zredlined/probe-gt-gauge-cluster-enclosure/reference/cage_scan/steering_support_detail_reference.png

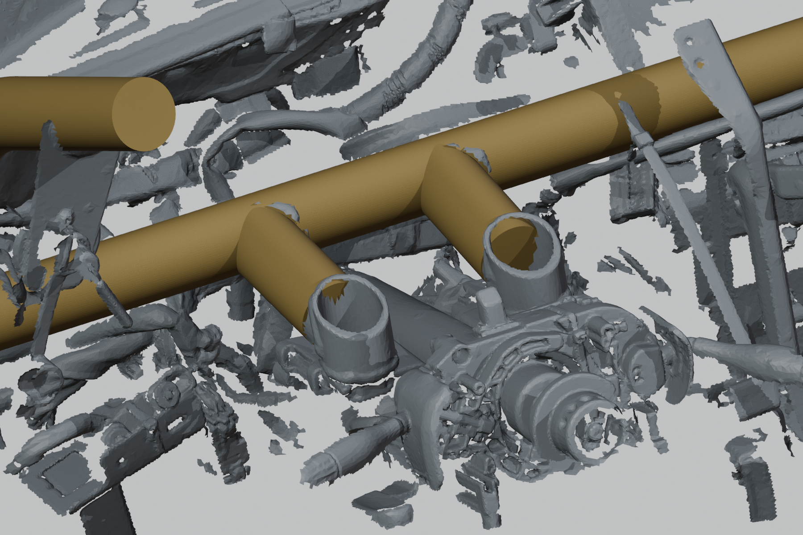
reference/cage_scan/steering_support_detail_reference.png
