zredlined/probe-gt-gauge-cluster-enclosure/reference/cage_scan/top_view_reference.png

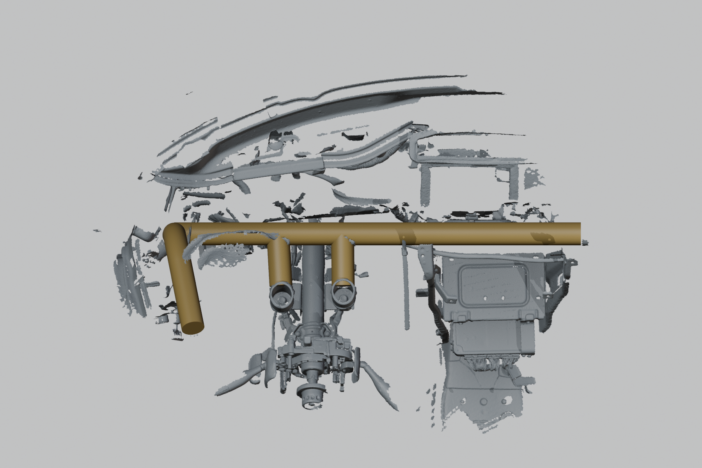
reference/cage_scan/top_view_reference.png
