zredlined/probe-gt-gauge-cluster-enclosure/reference/cluster_scan/mounting_hole_fits.png

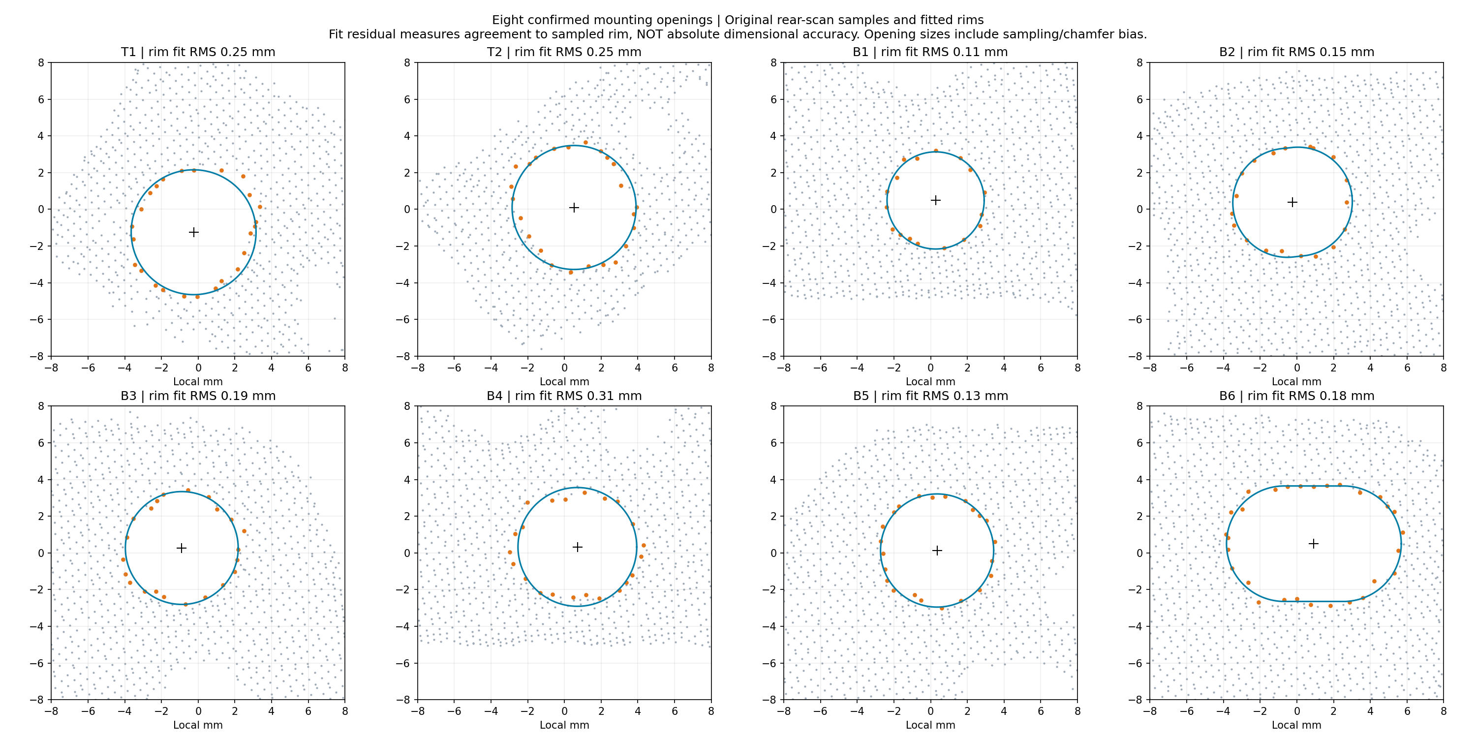
reference/cluster_scan/mounting_hole_fits.png
