zredlined/probe-gt-gauge-cluster-enclosure/reference/cluster_scan/mounting_holes_identification.png

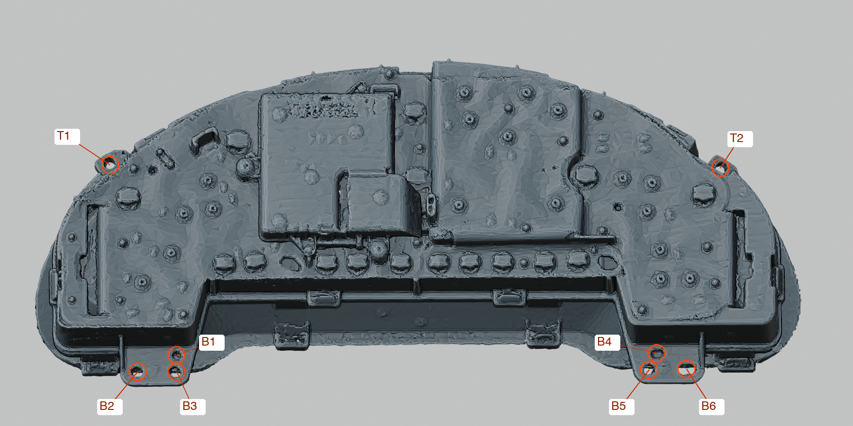
reference/cluster_scan/mounting_holes_identification.png
