zredlined/probe-gt-gauge-cluster-enclosure/stl/shell_L.stl

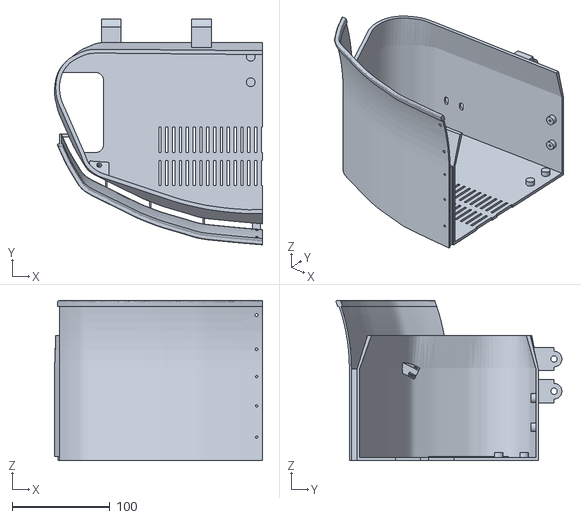
[picture p31: CAD file, 2026-10-02]
stl/shell_L.stl
213.1 x 231.3 x 164.0
