zredlined/probe-gt-gauge-cluster-enclosure/stl/test/test_coupon.stl

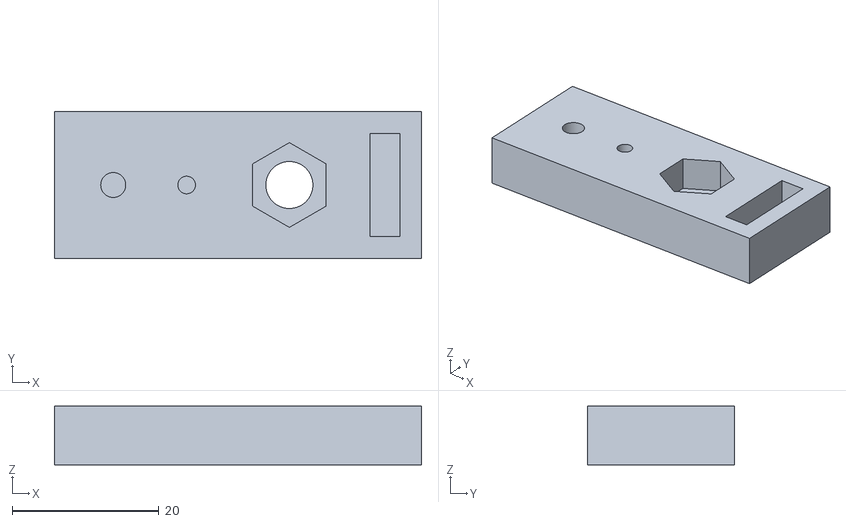
[picture p32: CAD file, 2026-09-27]
stl/test/test_coupon.stl
50.0 x 20.0 x 8.00
