zredlined/probe-gt-gauge-cluster-enclosure/reference/cage_scan/driver_side_steering_support_mm.stl

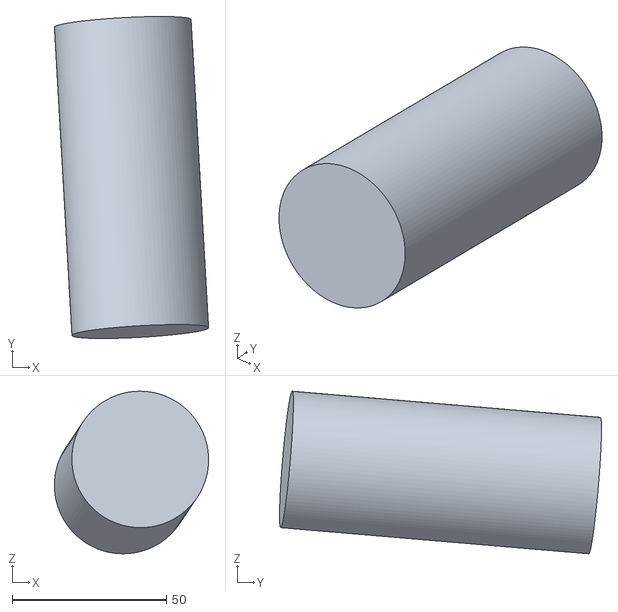
[picture p33: CAD file, 2026-09-26]
reference/cage_scan/driver_side_steering_support_mm.stl
50.1 x 104.5 x 52.8
