zredlined/probe-gt-gauge-cluster-enclosure/stl/shell_R.stl

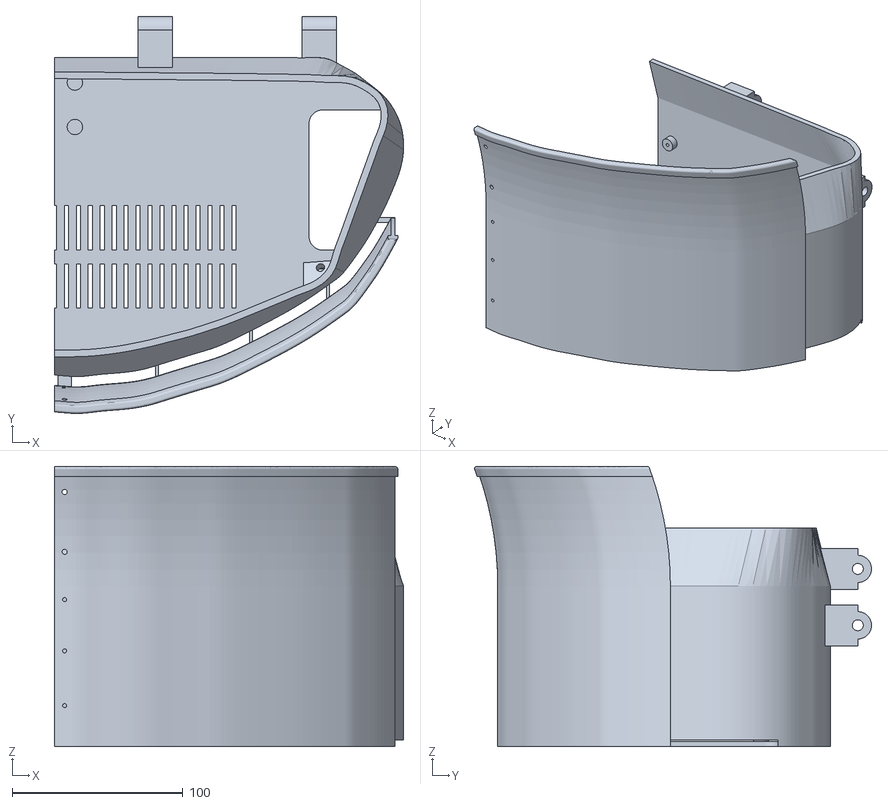
[picture p34: CAD file, 2026-10-02]
stl/shell_R.stl
204.3 x 232.2 x 164.0
