zredlined/probe-gt-gauge-cluster-enclosure/stl/support_pieces.3mf

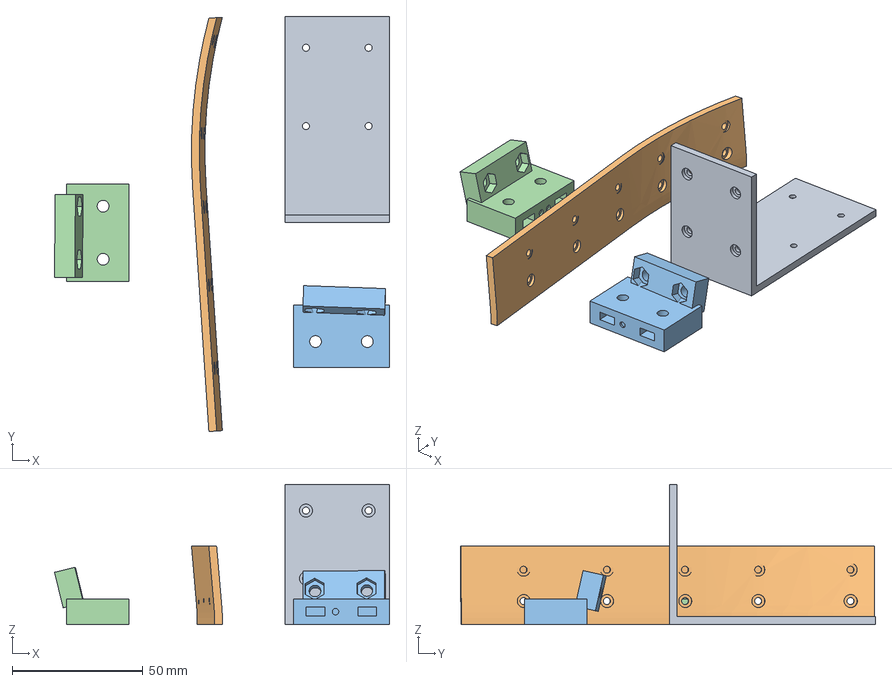
[picture p36: CAD file, 2026-10-02]
stl/support_pieces.3mf
128.3 x 159.0 x 53.7 mm
print_keel_bar.stl
print_spine_bar.stl
print_foot_lug_L.stl
print_foot_lug_R.stl
