zredlined/probe-gt-gauge-cluster-enclosure/reference/cage_scan/master_switch_region_scan_mm.stl

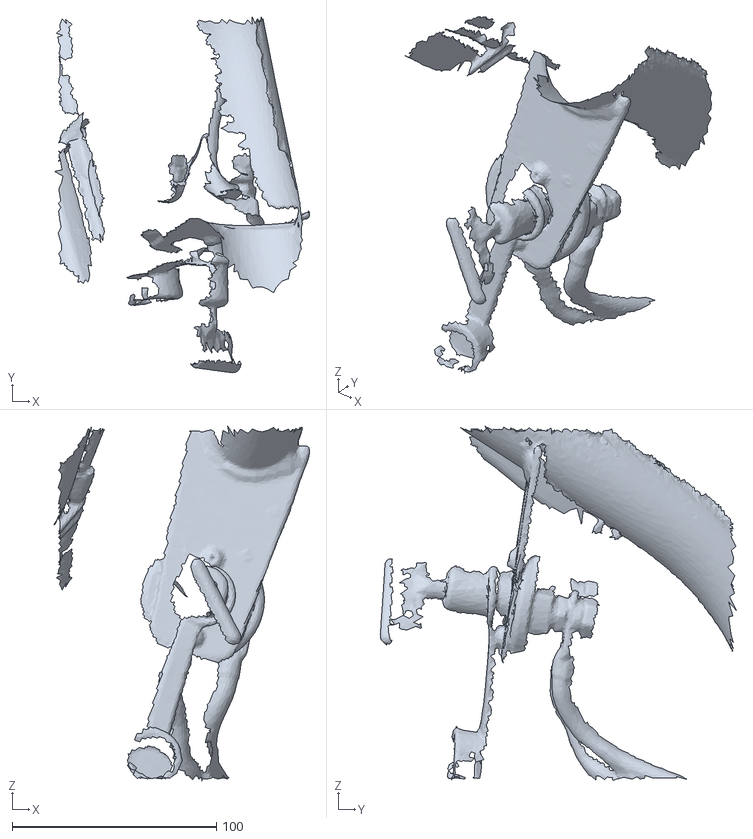
[picture p37: CAD file, 2026-09-26]
reference/cage_scan/master_switch_region_scan_mm.stl
125.0 x 174.5 x 173.8
