zredlined/probe-gt-gauge-cluster-enclosure/stl/foot_L.stl

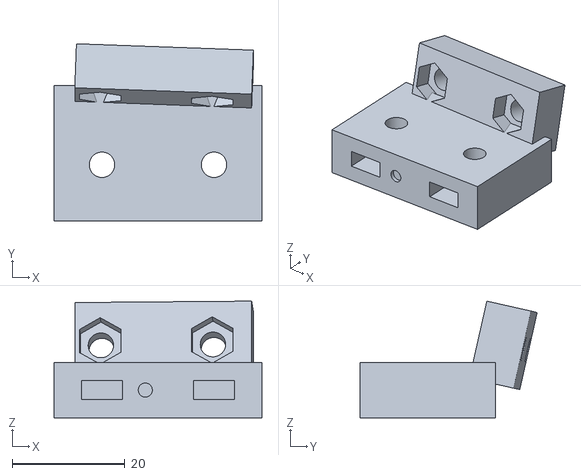
[picture p38: CAD file, 2026-09-30]
stl/foot_L.stl
36.8 x 31.4 x 20.7
