zredlined/probe-gt-gauge-cluster-enclosure/reference/cage_scan/cage_dash_crossbar_mm.stl

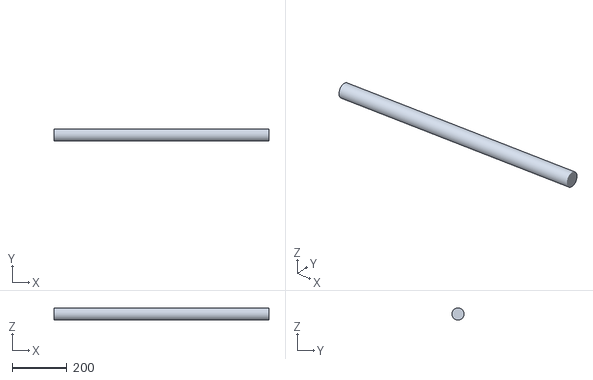
[picture p39: CAD file, 2026-09-26]
reference/cage_scan/cage_dash_crossbar_mm.stl
782.3 x 44.5 x 44.5
