zredlined/probe-gt-gauge-cluster-enclosure/stl/foot_R.stl

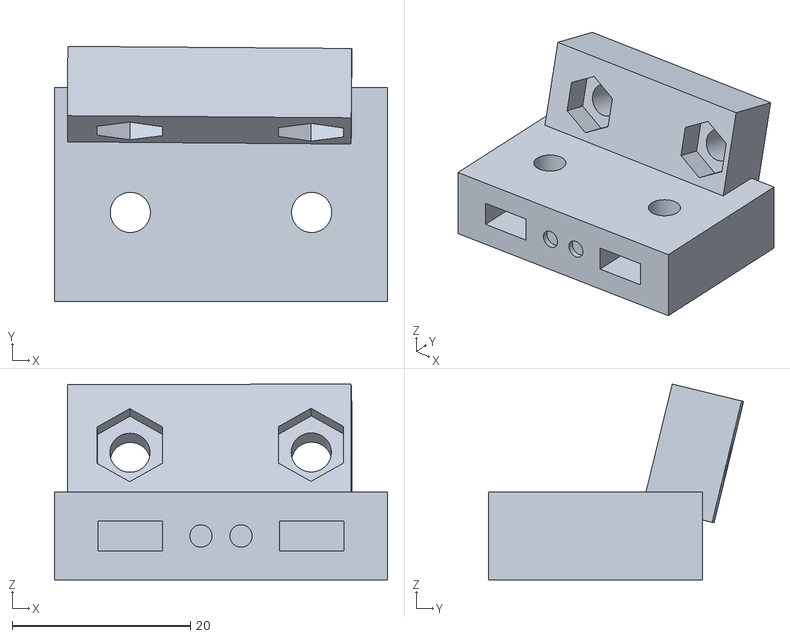
[picture p40: CAD file, 2026-09-30]
stl/foot_R.stl
37.3 x 28.6 x 22.0
