zredlined/probe-gt-gauge-cluster-enclosure/reference/cage_scan/cage_driver_upright_mm.stl

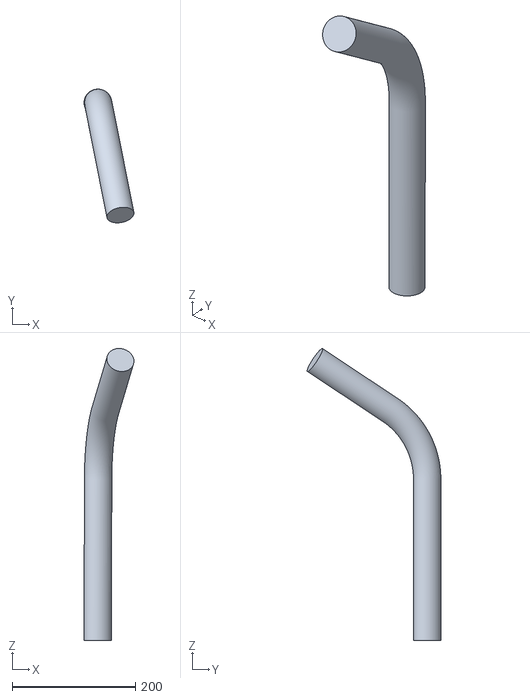
[picture p41: CAD file, 2026-09-26]
reference/cage_scan/cage_driver_upright_mm.stl
80.9 x 216.7 x 473.2
