zredlined/probe-gt-gauge-cluster-enclosure/stl/spine_bar.stl

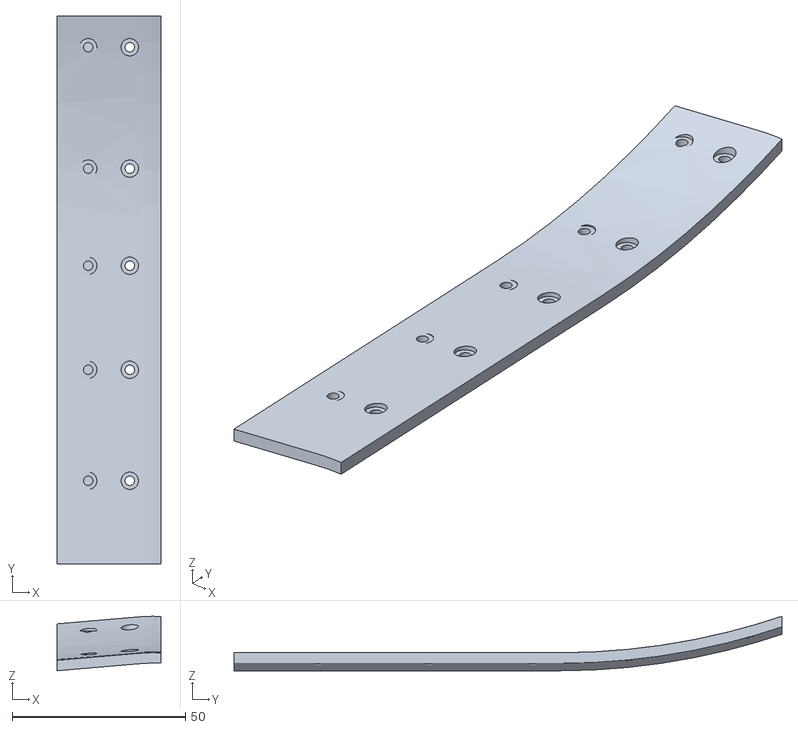
[picture p42: CAD file, 2026-09-30]
stl/spine_bar.stl
30.0 x 158.0 x 15.7
