zredlined/probe-gt-gauge-cluster-enclosure/reference/cage_scan/steering_supports_region_scan_mm.stl

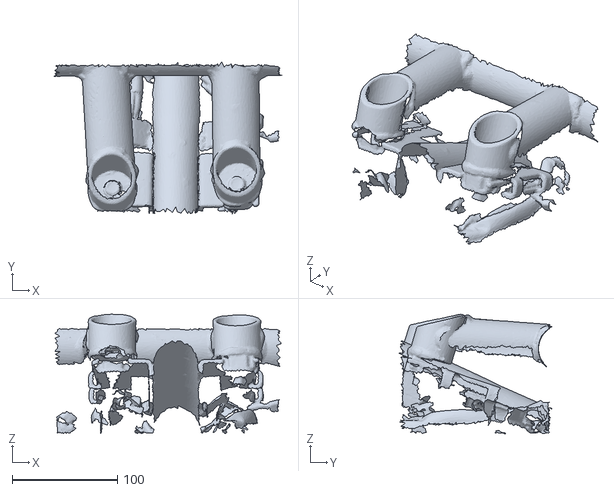
[picture p43: CAD file, 2026-09-26]
reference/cage_scan/steering_supports_region_scan_mm.stl
215.5 x 146.6 x 113.5
