zredlined/probe-gt-gauge-cluster-enclosure/stl/keel_bar.stl

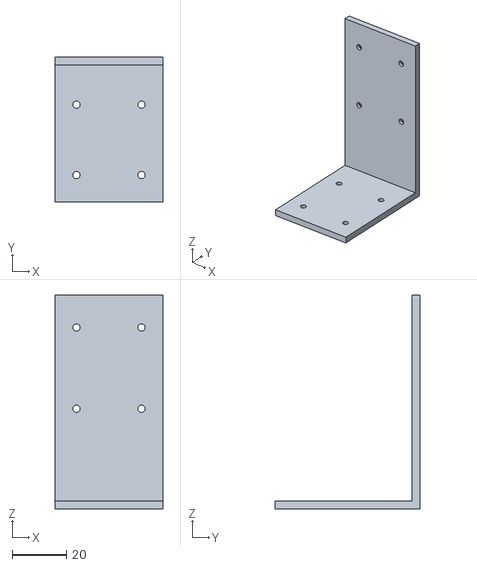
[picture p44: CAD file, 2026-09-28]
stl/keel_bar.stl
40.0 x 53.7 x 79.0
