zredlined/probe-gt-gauge-cluster-enclosure/reference/cage_scan/dash_context_mm.stl

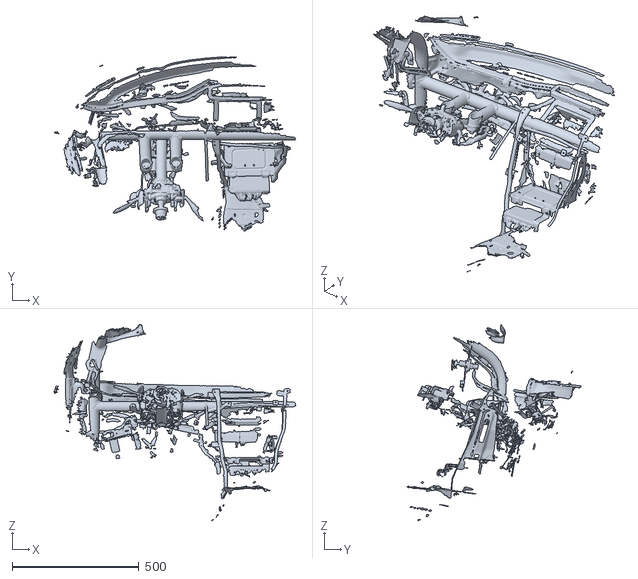
[picture p45: CAD file, 2026-09-26]
reference/cage_scan/dash_context_mm.stl
955.7 x 689.1 x 776.9
