zredlined/probe-gt-gauge-cluster-enclosure/stl/bar_clamp_lower_driver.stl

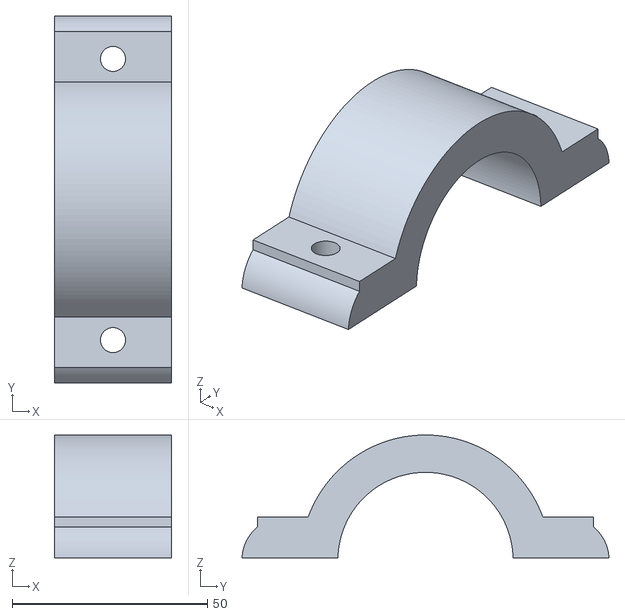
[picture p46: CAD file, 2026-09-27]
stl/bar_clamp_lower_driver.stl
30.0 x 94.0 x 31.5
