zredlined/probe-gt-gauge-cluster-enclosure/stl/arm_clamp_lower_driver.stl

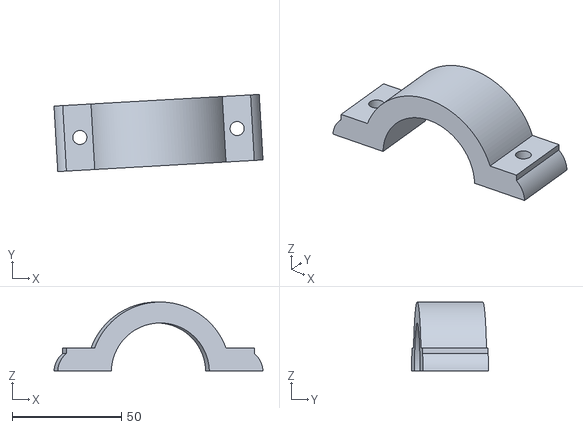
[picture p47: CAD file, 2026-09-27]
stl/arm_clamp_lower_driver.stl
95.5 x 35.3 x 31.5
