zredlined/probe-gt-gauge-cluster-enclosure/stl/arm_clamp_lower_center.stl

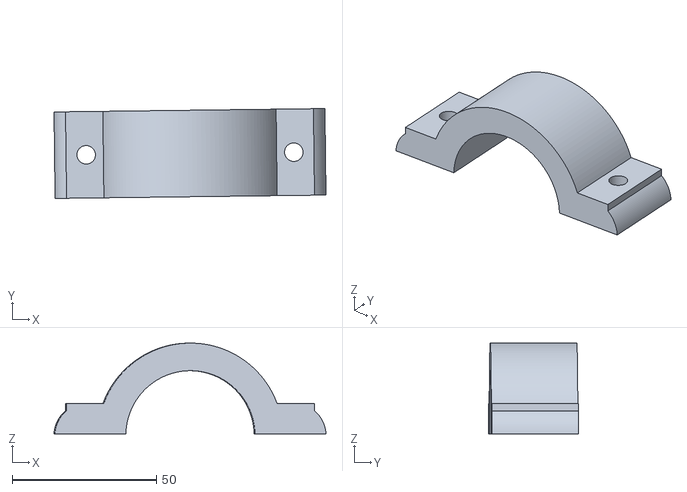
[picture p48: CAD file, 2026-09-27]
stl/arm_clamp_lower_center.stl
94.3 x 31.2 x 31.5
